sklosky-nl/sound-monitoring-mesh/sound level mesh hardware design.md

# Sound Level Mesh System - Hardware Design Document

## Document Information
- **Version:** 1.1
- **Date:** February 1, 2026
- **Status:** Production - Hardware Deployed
- **Author:** Hardware Engineering Team
- **Related Documents:** Sound Level Mesh System PRD, Architecture Document
- **Deployment Status:** Hardware received, assembled, and operational

---

## 1. Executive Summary

This document describes the hardware design for the Sound Level Mesh System monitoring devices. Each device consists of an ESP32-C3 microcontroller connected to an MH-ET LIVE INMP441 I2S Digital Microphone Module. The system requires 10 identical monitoring devices communicating via WiFi to a central web server.

### Hardware Components
- **Microcontroller:** ESP32-C3 Development Board (4MB flash)
- **Microphone Module:** MH-ET LIVE INMP441 I2S Digital Microphone Module
- **Power Supply:** USB Wall Charger Adapter (5V)
- **Power Cable:** USB-C Charging Cable
- **Enclosure:** Weather-resistant housing (to be determined)

### Purchased Hardware Status

**Hardware has been purchased and is awaiting delivery (Order Date: January 4, 2026).**

**Purchased Components:**
- ✅ **ESP32-C3 Development Boards:** 10 units (Simple Robot Store)
  - Model: ESP32-C3 Super Mini Development Board
  - Flash: 4MB
  - WiFi + Bluetooth
  - Total Cost: $21.79
  
- ✅ **MH-ET LIVE INMP441 I2S Microphone Modules:** 10 units (YX Electronic Components)
  - Omnidirectional MEMS microphone
  - I2S digital interface
  - Total Cost: $21.90 (10 × $2.19)
  
- ✅ **USB Wall Charger Adapters:** 10 units (Singyo Store)
  - 5 Pack × 2 orders = 10 total units
  - US Plug, Fast Charging
  - Total Cost: $8.62 (2 × $4.55)
  
- ✅ **USB-C Charging Cables:** 12 units (Super Deals Wholesale Factory Store)
  - 3 Pack × 4 orders = 12 total units
  - 1M length, 6A 100W Type C
  - Total Cost: $7.41 (4 × $1.99)

**Total Hardware Cost:** ~$59.72

**Note:** ESP32-C3 is a RISC-V based single-core microcontroller, different from the dual-core Xtensa-based ESP32. The specifications and pin assignments in this document will need to be verified against the ESP32-C3's actual capabilities and pinout.

---

## 2. Component Specifications

### 2.1 ESP32-C3 Microcontroller

#### Purchased Development Board
- **Model:** ESP32-C3 Super Mini Development Board (Purchased)
- **Chip:** ESP32-C3
- **Processor:** 
  - Single-core RISC-V microprocessor
  - Clock frequency: 160 MHz
  - 32-bit RISC-V architecture
- **Memory:**
  - Flash: 4 MB (as purchased)
  - SRAM: 400 KB
  - ROM: 384 KB
- **WiFi:**
  - 802.11 b/g/n (2.4 GHz)
  - WPA2/WPA3 support
- **Bluetooth:** Bluetooth 5.0 LE
- **GPIO Pins:** 21 programmable GPIO pins
- **I2S Interface:** Built-in I2S peripheral (to be verified)
- **Power:**
  - Operating voltage: 3.3V
  - Input voltage: 5V (via USB-C)
  - Current consumption: ~80-160 mA (active), ~10 µA (deep sleep)
- **USB:** USB-C interface
- **Dimensions:** Smaller form factor than standard ESP32 DevKit

**Important Note:** ESP32-C3 uses a different architecture (RISC-V) and has different pin assignments than the standard ESP32. The I2S pin assignments and GPIO numbers will need to be verified against the specific ESP32-C3 board's pinout once hardware is received.

#### ESP32-C3 Pinout (Relevant Pins - To Be Verified)

**Note:** Pin assignments below are preliminary and must be verified against the actual ESP32-C3 Super Mini board pinout once hardware is received.

- **Power Pins:**
  - USB-C: 5V input (via USB-C cable)
  - 3.3V: 3.3V output (if available on board)
  - GND: Ground
- **I2S Pins (for INMP441 connection - to be verified):**
  - I2S_DATA: TBD (verify GPIO pin)
  - I2S_WS: TBD (verify GPIO pin)
  - I2S_BCLK: TBD (verify GPIO pin)
- **Other Useful Pins:**
  - Boot button: TBD (verify GPIO pin)
  - Built-in LED: TBD (verify GPIO pin, if available)

**Action Required:** Once hardware is received, verify I2S peripheral availability and GPIO pin assignments for the ESP32-C3 Super Mini board.

### 2.2 MH-ET LIVE INMP441 I2S Digital Microphone Module

#### Module Specifications
- **Microphone Type:** Omnidirectional MEMS (Micro-Electro-Mechanical Systems)
- **Interface:** I2S digital output
- **Operating Voltage:** 1.8V - 3.3V (typically 3.3V)
- **Current Consumption:** ~1.2 mA typical
- **Sample Rate:** Up to 48 kHz
- **Bit Depth:** 24-bit
- **Signal-to-Noise Ratio (SNR):** 65 dB
- **Sensitivity:** -26 dBFS
- **Frequency Response:** 60 Hz - 15 kHz
- **Directional Pattern:** Omnidirectional
- **Operating Temperature:** -40°C to +85°C
- **Dimensions:** ~20mm × 20mm (module size)

#### Module Pinout
- **VDD:** Power supply (3.3V)
- **GND:** Ground
- **SCK:** Serial Clock (I2S Bit Clock)
- **WS:** Word Select (I2S Left/Right Clock)
- **SD:** Serial Data (I2S Data Output)
- **L/R:** Left/Right channel select (connect to GND for left/mono)

---

## 3. Wiring Diagram and Connections

### 3.1 INMP441 to ESP32-C3 Connection

**✅ Verified and Tested Configuration - Production Ready (February 2026)**

Pin assignments have been implemented, tested in firmware, and confirmed operational. System is actively deployed with "Sensor 01" transmitting measurements every 5 seconds at 76-77 dB ambient levels.

```
INMP441 Module          ESP32-C3 Board
─────────────────       ────────────────
VDD              ──────> 3.3V
GND              ──────> GND
SCK              ──────> GPIO 5 (I2S_BCLK)
WS               ──────> GPIO 6 (I2S_WS)
SD               ──────> GPIO 4 (I2S_DATA)
L/R              ──────> GND (for mono/left channel)
```

**Deployment Status:**
- ESP32-C3 Super Mini: ✅ Operational via USB-C power
- INMP441 Module: ✅ Wired and functional
- I2S Communication: ✅ Verified (16kHz sample rate, 32-bit containers)
- Audio Sampling: ✅ Active (76-77 dB ambient sound levels measured)
- WiFi Connectivity: ✅ Connected to backend server at 192.168.68.57:3000
- Configuration System: ✅ Dynamic config fetch on startup and periodic refresh
- Power: USB-C wall charger (from purchased batch)
- Device ID: "Sensor 01" (note: requires URL encoding for spaces)

**Important Notes for Additional Deployments:**
- Device IDs with spaces require URL encoding (%20) in firmware
- Configuration fetched automatically on startup from server
- Periodic configuration refresh every 100 measurements (~5 minutes)
- Default frequency bands: 20-200Hz, 200-2000Hz, 2000-8000Hz
- Per-device calibration offset applied (currently 1.0 dB for "Sensor 01")

### 3.2 Detailed Pin Connections (Verified)

| INMP441 Pin | ESP32-C3 Pin | Function | Notes |
|---|---|---|---|
| VDD | 3.3V | Power Supply | Connect to 3.3V output pin on ESP32-C3 board |
| GND | GND | Ground | Common ground |
| SCK | GPIO 5 | I2S Bit Clock | I2S_BCK - Serial Clock |
| WS | GPIO 6 | I2S Word Select | I2S_WS - Left/Right Clock |
| SD | GPIO 4 | I2S Serial Data | I2S_DATA - Serial Data Input |
| L/R | GND | Channel Select | Ground for left/mono channel |

**Status:** ✅ Verified and implemented in firmware. I2S peripheral confirmed functional on ESP32-C3.

### 3.3 Power Connections

**Option 1: USB Power (Recommended for Development)**
- Connect USB cable to ESP32 DevKit USB port
- Provides 5V power, regulated to 3.3V on board
- INMP441 powered from ESP32's 3.3V pin

**Option 2: External Power Supply**
- Connect 5V power supply to ESP32 VIN pin
- Ensure power supply can provide at least 500 mA
- INMP441 powered from ESP32's 3.3V pin

**Power Consumption Estimate:**
- ESP32 (active): ~80-260 mA @ 3.3V
- INMP441: ~1.2 mA @ 3.3V
- **Total:** ~100-270 mA @ 3.3V (or ~150-400 mA @ 5V input)

### 3.4 Wiring Diagram (Schematic View)

```
                    ┌─────────────────┐
                    │   ESP32 DevKit  │
                    │                 │
     USB/5V ───────>│ VIN             │
                    │                 │
                    │ 3.3V ───────────┼───┐
                    │                 │   │
                    │ GND ────────────┼───┼───┐
                    │                 │   │   │
                    │ GPIO 5 (BCLK) ──┼───┼───┼───┐
                    │                 │   │   │   │
                    │ GPIO 6 (WS) ────┼───┼───┼───┼───┐
                    │                 │   │   │   │   │
                    │ GPIO 4 (DATA) ──┼───┼───┼───┼───┼───┐
                    │                 │   │   │   │   │   │
                    └─────────────────┘   │   │   │   │   │
                                          │   │   │   │   │
                    ┌─────────────────┐  │   │   │   │   │
                    │  INMP441 Module  │  │   │   │   │   │
                    │                  │  │   │   │   │   │
                    │ VDD <────────────┘  │   │   │   │   │
                    │ GND <───────────────┘   │   │   │   │
                    │ SCK <────────────────────┘   │   │   │
                    │ WS  <───────────────────────┘   │   │
                    │ SD  <────────────────────────────┘   │
                    │ L/R <────────────────────────────────┘
                    │                  │
                    └──────────────────┘
```

---

## 4. Physical Layout and Assembly

### 4.1 Component Placement

**Recommended Layout:**
1. ESP32 DevKit board mounted on standoffs or PCB
2. INMP441 module positioned to minimize wire length
3. Keep I2S signal wires as short as possible (< 10 cm recommended)
4. Route power and ground wires together to reduce noise
5. Separate digital signals from power lines

### 4.2 Wire Specifications

**For I2S Signals (SCK, WS, SD):**
- **Type:** Twisted pair or shielded cable recommended
- **Length:** Keep under 10 cm if possible
- **Gauge:** 22-24 AWG
- **Shielding:** Optional but recommended for longer runs

**For Power (VDD, GND):**
- **Type:** Standard hookup wire
- **Length:** As needed for layout
- **Gauge:** 22-24 AWG
- **Note:** Use thicker wire (20 AWG) if power supply is far from module

### 4.3 Soldering vs. Breadboard

**Development/Prototyping:**
- Use breadboard or jumper wires for initial testing
- Allows easy reconfiguration and debugging

**Production:**
- Solder connections for reliability
- Use header pins or direct soldering
- Consider custom PCB for final design

### 4.4 Assembly Steps

**Note:** These steps assume ESP32-C3 I2S pin assignments have been verified. Pin numbers are placeholders until hardware is received.

1. **Prepare ESP32-C3:**
   - Ensure ESP32-C3 board is powered off
   - Identify I2S GPIO pins (to be verified), 3.3V output, and GND
   - Review ESP32-C3 Super Mini board pinout documentation

2. **Prepare INMP441:**
   - Identify module pins (VDD, GND, SCK, WS, SD, L/R)
   - Ensure module is clean and undamaged
   - Verify module is from purchased batch

3. **Make Connections:**
   - Connect power first: VDD to 3.3V, GND to GND
   - Connect I2S signals: SCK→GPIO 5, WS→GPIO 6, SD→GPIO 4
   - Connect L/R to GND for mono operation
   - Use purchased jumper wires for connections

4. **Verify Connections:**
   - Double-check all connections
   - Ensure no short circuits
   - Verify power polarity
   - Reference ESP32-C3 pinout diagram

5. **Power On:**
   - Connect USB-C cable to ESP32-C3
   - Connect USB-C cable to purchased wall charger
   - Plug wall charger into power outlet
   - Check for proper operation

---

## 5. I2S Configuration

### 5.1 I2S Bus Configuration

**For INMP441 Module:**
- **Sample Rate:** 16 kHz (recommended) or up to 48 kHz
- **Bit Depth:** 24-bit
- **Channel Format:** Mono (left channel)
- **Communication Format:** I2S (standard)
- **Bit Order:** MSB first
- **Clock Polarity:** Normal (data on falling edge)

### 5.2 ESP32 I2S Peripheral Settings

**I2S Configuration Parameters:**
- **Mode:** I2S_MODE_MASTER | I2S_MODE_RX (receive mode)
- **Sample Rate:** 16000 Hz (or 48000 Hz)
- **Bits Per Sample:** I2S_BITS_PER_SAMPLE_24BIT
- **Channel Format:** I2S_CHANNEL_FMT_ONLY_LEFT (mono)
- **Communication Format:** I2S_COMM_FORMAT_STAND_I2S
- **DMA Buffer Count:** 8
- **DMA Buffer Length:** 1024 bytes

### 5.3 Clock Configuration

**I2S Clock Calculation:**
- Bit Clock (BCLK) = Sample Rate × Bits Per Sample × Channels
- For 16 kHz, 24-bit, mono: BCLK = 16000 × 24 × 1 = 384 kHz
- For 48 kHz, 24-bit, mono: BCLK = 48000 × 24 × 1 = 1.152 MHz

**ESP32 I2S Clock:**
- ESP32 generates I2S clock internally
- Configure using I2S driver API
- Clock accuracy depends on APB clock (typically 80 MHz)

---

## 6. Power Supply Design

### 6.1 Power Requirements

**Total System Power:**
- ESP32-C3: 80-160 mA @ 3.3V (active mode)
- INMP441: 1.2 mA @ 3.3V
- **Total:** ~100-170 mA @ 3.3V

**Purchased Power Supply:**
- **USB Wall Charger Adapters:** 10 units purchased
  - 5V output via USB port
  - Fast charging capable
  - US Plug
  - Sufficient for ESP32-C3 + INMP441 power requirements

**Input Power:**
1. **USB-C Cable + Wall Charger (Purchased):** 
   - USB-C cable (1M, 6A 100W capable) connects ESP32-C3 to wall charger
   - Wall charger provides 5V power
   - 12 cables purchased (2 extra for spares)

### 6.2 Power Supply Considerations

**Voltage Regulation:**
- ESP32 DevKit includes onboard 3.3V regulator
- Accepts 5V input, regulates to 3.3V
- INMP441 requires stable 3.3V supply

**Power Filtering:**
- Add decoupling capacitors near INMP441:
  - 100 nF ceramic capacitor (VDD to GND)
  - 10 µF electrolytic capacitor (optional, for stability)

**Power Consumption Optimization:**
- ESP32 can enter light sleep between measurements
- Reduces average power consumption
- INMP441 remains active during sleep (low power)

### 6.3 Battery Operation (Optional)

**If Battery-Powered:**
- Use 3.7V Li-ion battery (single cell)
- Requires voltage regulator to 3.3V
- Add battery management circuit (BMS)
- Consider power consumption for battery life calculation

---

## 7. Enclosure and Environmental Considerations

### 7.1 Enclosure Requirements

**Physical Protection:**
- Weather-resistant housing (IP54 minimum, IP65 recommended)
- Protection from dust and moisture
- Ventilation for microphone (acoustic port)
- Access to USB port or power connector

**Acoustic Considerations:**
- Microphone should have clear path to environment
- Acoustic port/opening for sound waves
- Avoid blocking microphone with enclosure material
- Consider wind protection (foam windscreen)

**Thermal Management:**
- ESP32 can generate heat during operation
- Ensure adequate ventilation
- Operating temperature: 0°C to +50°C (typical)

### 7.2 Mounting Considerations

**Installation:**
- Secure mounting to prevent vibration
- Position microphone away from noise sources
- Consider height and orientation for optimal sound capture
- Ensure WiFi antenna has clear line of sight

**Cable Management:**
- Secure power cable to prevent disconnection
- Protect cables from environmental damage
- Use weather-resistant cable if exposed

---

## 8. Testing and Verification

### 8.1 Initial Testing

**Power-On Test:**
1. Connect power supply
2. Verify ESP32 boots (LED indicators if available)
3. Check WiFi connectivity
4. Verify I2S communication with INMP441

**Audio Test:**
1. Send test signal or use known sound source
2. Verify audio data is received via I2S
3. Check sample rate and bit depth
4. Verify FFT processing produces expected results

### 8.2 Functional Testing

**Measurement Accuracy:**
- Compare with calibrated reference sound level meter
- Test at various sound levels (30-130 dB)
- Verify frequency band measurements
- Test calibration offset application

**System Integration:**
- Verify data transmission to central server
- Test configuration retrieval
- Verify real-time monitoring
- Test device registration

### 8.3 Environmental Testing

**Temperature:**
- Test at operating temperature range
- Verify performance at extremes

**Humidity:**
- Test in high humidity conditions
- Verify enclosure protection

**Vibration:**
- Test with mechanical vibration
- Verify connections remain secure

---

## 9. Bill of Materials (BOM)

### 9.1 Required Components (Per Device)

| Component | Part Number/Description | Quantity | Status |
|---|---|---|---|
| ESP32-C3 Board | ESP32-C3 Super Mini (4MB flash) | 1 | ✅ Purchased (10 units) |
| INMP441 Module | MH-ET LIVE INMP441 | 1 | ✅ Purchased (10 units) |
| USB-C Cable | Type C, 1M, 6A 100W | 1 | ✅ Purchased (12 units total) |
| USB Wall Charger | 5V Fast Charging, US Plug | 1 | ✅ Purchased (10 units) |
| Jumper Wires | 22-24 AWG | 6 | ⏳ To be purchased |
| Enclosure | Weather-resistant | 1 | ⏳ To be determined |
| Standoffs | M3, 10mm | 4 | ⏳ Optional, to be purchased |

**Purchased Hardware Summary:**
- ✅ All 10 ESP32-C3 development boards
- ✅ All 10 INMP441 microphone modules
- ✅ All 10 USB wall chargers (with 2 extra cables)
- ⏳ Jumper wires and enclosures still needed

### 9.2 Optional Components

| Component | Description | Quantity | Notes |
|---|---|---|---|
| Decoupling Capacitors | 100 nF ceramic | 2 | Power filtering |
| LED Indicator | 3mm LED | 1 | Status indication |
| Resistor | 220Ω | 1 | For LED (if used) |
| Antenna Extension | WiFi antenna cable | 1 | If needed for range |

### 9.3 Tools Required

- Soldering iron (if soldering connections)
- Multimeter (for testing)
- Wire strippers
- Breadboard (for prototyping)
- Oscilloscope (optional, for signal verification)

---

## 10. Troubleshooting

### 10.1 Common Issues

**No Audio Data:**
- Check I2S pin connections
- Verify I2S configuration matches INMP441 specs
- Check power supply to INMP441 (3.3V)
- Verify sample rate and bit depth settings

**Poor Audio Quality:**
- Check for loose connections
- Verify power supply stability
- Check for electrical interference
- Ensure proper I2S clock configuration

**WiFi Connection Issues:**
- Verify WiFi credentials
- Check signal strength
- Ensure ESP32 antenna is not blocked
- Verify network configuration

**Power Issues:**
- Check power supply voltage
- Verify current capacity (minimum 500 mA)
- Check for short circuits
- Verify ground connections

### 10.2 Diagnostic Procedures

**I2S Signal Verification (if I2S available on ESP32-C3):**
1. Verify I2S peripheral is available on ESP32-C3
2. Use oscilloscope to check I2S signals (if available)
3. Verify clock frequency matches configuration
4. Check data signal for activity
5. Verify word select timing

**Power Verification:**
1. Measure voltage at INMP441 VDD pin (should be 3.3V)
2. Check current consumption
3. Verify no voltage drops under load

**Communication Test:**
1. Use serial monitor to check ESP32-C3 output
2. Verify I2S data reception (if I2S peripheral available)
3. Check for error messages
4. Test WiFi connectivity
5. Test data transmission to server

---

## 11. Safety Considerations

### 11.1 Electrical Safety

- Ensure proper power supply voltage (5V for ESP32, 3.3V for INMP441)
- Avoid short circuits between power and ground
- Use appropriate wire gauge for current requirements
- Verify polarity before connecting power

### 11.2 Environmental Safety

- Ensure enclosure provides adequate protection
- Avoid exposure to water or excessive moisture
- Protect from extreme temperatures
- Secure mounting to prevent falling

### 11.3 Operational Safety

- Follow manufacturer specifications
- Do not exceed maximum ratings
- Allow adequate ventilation for heat dissipation
- Regular inspection and maintenance

---

## 12. Future Enhancements

### 12.1 Potential Improvements

- **Custom PCB:** Design dedicated PCB for production
- **Battery Power:** Add battery support with power management
- **Additional Sensors:** Temperature, humidity sensors
- **Status LEDs:** Visual indicators for device status
- **External Antenna:** Improved WiFi range
- **Power Management:** Low-power modes for extended operation

### 12.2 Scalability Considerations

- Design for easy assembly and maintenance
- Standardize connections for consistency
- Document assembly procedures
- Create assembly jigs if producing multiple units

---

## 13. Appendix

### A. Pin Reference Tables

**ESP32-C3 GPIO Pin Functions (Verified):**
- I2S_DATA: GPIO 4 (Input) - Serial Data from INMP441
- I2S_BCLK: GPIO 5 (Output) - Bit Clock to INMP441
- I2S_WS: GPIO 6 (Output) - Word Select to INMP441
- Boot button: GPIO 9 (Input, pull-up) - Standard on ESP32-C3
- Built-in LED: GPIO 8 (Output) - Standard on ESP32-C3 Super Mini

**Note:** Pin assignments verified and implemented in firmware. I2S peripheral confirmed functional on ESP32-C3.

**INMP441 Pin Functions:**
- VDD: Power (3.3V)
- GND: Ground
- SCK: Serial Clock (Input)
- WS: Word Select (Input)
- SD: Serial Data (Output)
- L/R: Channel Select (Input, connect to GND)

### B. I2S Timing Diagram

```
BCLK:  _|‾|_|‾|_|‾|_|‾|_|‾|_|‾|_|‾|_|‾|_
       |   |   |   |   |   |   |   |   |
WS:    ‾‾‾‾‾‾‾‾‾‾‾‾‾‾‾‾‾‾‾‾‾‾‾‾‾‾‾‾‾‾‾‾
       (Left Channel)    (Right Channel)
SD:    MSB ────────────────> LSB
       (24-bit data word)
```

### C. References

- ESP32 Technical Reference Manual: Espressif Systems
- ESP-IDF Programming Guide: Espressif Systems
- INMP441 Datasheet: InvenSense
- MH-ET LIVE INMP441 Module Documentation
- I2S Bus Specification

### D. Related Documents

- Sound Level Mesh System PRD
- Sound Level Mesh Architecture Document
- Firmware Development Guide (to be created)
- Assembly Instructions (to be created)

---

## Document Approval

| Role | Name | Signature | Date |
|---|---|---|---|
| Hardware Engineer | | | |
| Electrical Engineer | | | |
| System Architect | | | |

---

**Document Status:** Draft - Pending Review and Approval
