sklosky-nl/sound-monitoring-mesh/PRE_COMMIT_CHECKLIST.md

# Pre-Commit Security Checklist

✅ **All sensitive information has been protected**

## Files Excluded from Git

### 1. WiFi Credentials & Configuration
- ✅ `firmware/sound-level-sensor/sdkconfig` - Contains WiFi SSID "YOUR_WIFI_SSID" and password
- ✅ Template provided: `sdkconfig.example` with safe defaults

### 2. Backend Data Directories
- ✅ `backend/data/devices/` - Device registration JSON files
- ✅ `backend/data/measurements/` - Measurement data files
- ✅ `backend/data/alerts/` - Alert configuration and history
- ✅ `backend/data/logs/` - Server log files

### 3. Other Sensitive Files
- ✅ `screenlog.0` - Terminal session log
- ✅ `.env` files - Environment variables

## Files Updated to Remove Sensitive Defaults

### Kconfig.projbuild
- ❌ **Before:** `CONFIG_WIFI_SSID="YOUR_WIFI_SSID"`
- ✅ **After:** `CONFIG_WIFI_SSID="YourWiFiSSID"`

- ❌ **Before:** `CONFIG_WIFI_PASSWORD="REDACTED"`
- ✅ **After:** `CONFIG_WIFI_PASSWORD="YourWiFiPassword"`

- ❌ **Before:** `CONFIG_SERVER_URL="http://192.168.68.67:3000"`
- ✅ **After:** `CONFIG_SERVER_URL="http://192.168.1.100:3000"` (generic)

## New Security Documentation

### SECURITY.md
- Complete guide for securing the project
- Setup instructions for new users
- What's safe to commit vs. what to exclude
- Recovery procedures for accidentally committed secrets

### README.md
- Added 🔒 Security section
- Links to SECURITY.md
- Setup instructions

### sdkconfig.example
- Template configuration file
- Safe placeholder values
- Instructions for users to copy and configure

## Gitignore Patterns Added

```gitignore
# ESP32 configuration (contains WiFi credentials)
firmware/**/sdkconfig
firmware/**/sdkconfig.old
!firmware/**/sdkconfig.defaults

# Backend data directories
backend/data/measurements/
backend/data/devices/
backend/data/alerts/
backend/data/logs/

# Screen logs
screenlog.*
```

## Verification Commands

Run these before committing:

```bash
# Check what files git will track
git status

# Verify sdkconfig is ignored
git check-ignore firmware/sound-level-sensor/sdkconfig
# Should output: firmware/sound-level-sensor/sdkconfig

# Search for any passwords or SSIDs in tracked files
git grep -i "YOUR_WIFI_SSID\|REDACTED" -- ':!.gitignore' ':!*.md'
# Should return no results

# Check what would be added
git add -n .
```

## Safe to Commit

✅ All source code files (*.c, *.js, *.html, *.css)
✅ Configuration templates (sdkconfig.example, sdkconfig.defaults)
✅ Documentation files (*.md)
✅ Package manifests (package.json, CMakeLists.txt)
✅ Build scripts

## Status: READY FOR PUBLIC GITHUB ✅

All sensitive information has been:
- Excluded via .gitignore
- Replaced with safe defaults in templates
- Documented in SECURITY.md

**The repository is now safe to commit to a public GitHub repository.**
