sklosky-nl/sound-monitoring-mesh/enclosure/WIFI_SIGNAL_SOLUTIONS.md

# WiFi Signal Solutions for PETG Enclosure

> **✅ FINAL SOLUTION IMPLEMENTED:** After analysis and testing, the project uses **microphone foam windscreens** as the complete enclosure. This simple solution provides dust protection, RF transparency (<0.5 dB loss), acoustic transparency, and costs ~$1-2 per device. See [README.md](README.md) for implementation details.
>
> This document is retained for reference on RF attenuation issues and alternative solutions that were considered.

---

## Problem
PETG enclosures can block WiFi signals (2.4 GHz), especially when fully enclosed. This causes connectivity issues for ESP32 devices in dusty environments.

## Root Cause
- PETG attenuates 2.4 GHz signals by 3-8 dB per wall thickness
- Fully enclosed design creates partial Faraday cage effect
- ESP32-C3 has PCB antenna requiring clear RF path

---

## Solutions (Ranked by Effectiveness)

### 🥇 Solution 1: External Antenna (Most Reliable)
**Best for harsh dusty environments**

**Implementation:**
1. Add U.FL/IPEX connector to ESP32-C3
2. Route antenna cable through sealed cable gland (PG7, 3mm)
3. Mount 2.4 GHz antenna outside enclosure
4. Maintains full IP65+ dust/waterproof rating

**Parts Needed:**
- U.FL/IPEX to RP-SMA pigtail cable (10cm) - $3
- 2.4 GHz WiFi antenna with RP-SMA - $4
- PG7 cable gland - $2
- Total: ~$9/device

**Pros:**
- ✅ Full signal strength maintained
- ✅ Keeps complete dust seal
- ✅ Works in extreme environments
- ✅ Professional solution

**Cons:**
- ⚠️ Requires antenna connector soldering
- ⚠️ Slightly more complex assembly

---

### 🥈 Solution 2: RF Window in Enclosure
**Good balance of dust protection and signal**

**Implementation:**
1. Modify STL/F3D: Cut 30mm × 30mm opening above ESP32 location
2. Cover with thin polycarbonate sheet (0.5mm) or fine mesh
3. Seal edges with silicone gasket or adhesive
4. Maintains dust protection with <1 dB signal loss

**Design Changes:**
```
Enclosure modifications:
- Top panel: 30×30mm cutout centered over ESP32
- Add retaining lip for cover material
- Use stainless steel mesh (40-60 mesh) OR
- Use thin polycarbonate/acrylic window
```

**Pros:**
- ✅ No electronics modification needed
- ✅ Maintains most dust protection
- ✅ Simple implementation
- ✅ Minimal signal loss

**Cons:**
- ⚠️ Requires enclosure redesign/modification
- ⚠️ Slight dust ingress potential at window

---

### 🥉 Solution 3: Ventilation with Dust Filtering
**For moderate dust environments**

**Implementation:**
1. Add 6-8 holes (10-15mm diameter) around top perimeter
2. Cover with one of:
   - Stainless steel mesh (250-425 micron / 40-60 mesh)
   - Gore-Tex membrane vent patches
   - Sintered metal dust filters
3. Position holes for cross-ventilation

**Recommended Mesh Specifications:**
- **Mesh size:** 40-60 mesh (250-425 micron openings)
- **Material:** Stainless steel 316 (corrosion resistant)
- **Installation:** Epoxy or hot-glue to inside of enclosure

**Pros:**
- ✅ Good RF transparency
- ✅ Allows heat dissipation
- ✅ Simple to implement
- ✅ No electronics changes

**Cons:**
- ⚠️ Fine dust can still enter over time
- ⚠️ Not suitable for very dusty environments
- ⚠️ Requires filter maintenance/replacement

---

### 🔧 Solution 4: Material Change
**For new builds**

**Instead of PETG, use:**
1. **ABS** - Better RF transparency, slightly less dust resistant
2. **PLA** - Good RF, but lower heat tolerance
3. **Polycarbonate** - Excellent RF transparency and durability
4. **Hybrid:** PETG base + thin ABS/PLA top section

**Print Settings for RF Transparency:**
- Thin walls (1-2 perimeters, 0.8-1.6mm)
- Minimal infill in RF critical areas (10-20%)
- Avoid thick solid sections near antenna

---

## Quick Verification Tests

### Test 1: Confirm Enclosure is Blocking Signal
1. Remove device from enclosure
2. Monitor backend logs: `tail -f backend/data/logs/combined.log | grep "POST /api/data"`
3. Device should reconnect within 30-60 seconds
4. If it reconnects → enclosure is the problem

### Test 2: Measure Signal Strength (if device has serial access)
```c
// Add to ESP32 firmware:
int8_t rssi = WiFi.RSSI();
ESP_LOGI(TAG, "WiFi RSSI: %d dBm", rssi);
```
- Good signal: -30 to -67 dBm
- Fair signal: -68 to -80 dBm  
- Poor signal: < -80 dBm (likely to disconnect)

### Test 3: Drill Test Holes
1. Drill 3-4 small holes (5mm) in top of enclosure
2. Monitor if device reconnects
3. If successful → proves ventilation solution will work

---

## Recommended Implementation Plan

### For Your Dusty Environment:

**Option A: Quick Fix (Today)**
1. Drill 8× 12mm holes in top/sides of current enclosure
2. Cover with stainless steel mesh (from hardware store)
3. Hot glue or epoxy mesh in place
4. Cost: $5, Time: 30 minutes

**Option B: Professional Solution (Best Long-term)**
1. Order external antenna kit (~$10)
2. Solder U.FL connector to ESP32 (or use pre-made version)
3. Modify enclosure with cable gland pass-through
4. Mount antenna on exterior
5. Cost: $10/device, Time: 45 minutes per device

**Option C: Redesign Enclosure (For multiple devices)**
1. Modify .f3d design with RF window or ventilation
2. Add mesh/filter mounting features
3. Print new enclosures for all devices
4. Cost: ~$3-5/device (filament + mesh)
5. Time: 2 hours design + printing time

---

## Stainless Steel Mesh Specifications

**Recommended Mesh for Dust Protection + RF Transparency:**
- **Type:** Woven wire mesh
- **Material:** Stainless steel 316 or 304
- **Mesh Count:** 40-60 mesh (40-60 wires per inch)
- **Wire Diameter:** 0.18-0.25mm
- **Opening Size:** 250-425 microns
- **Blocks:** Particles > 250 microns (most dust)
- **Passes:** 2.4 GHz WiFi signals (wavelength: 125mm)

**Where to Buy:**
- Amazon: "40 mesh stainless steel screen"
- McMaster-Carr: Part #9318T53
- Local hardware store: Stainless steel window screen

---

## Notes from Build Experience

⚠️ **Discovered Issues:**
- Lid fit required heat gun adjustment (mentioned in main README)
- PETG thickness needed for dust protection blocks WiFi
- ESP32-C3 SuperMini uses PCB antenna (surface mount, no external connector stock)

**Lessons Learned:**
- Test RF connectivity BEFORE final enclosure design
- Consider antenna placement in CAD design phase
- Ventilation is always better than complete sealing for electronics
- PETG is great for mechanical parts, poor for RF applications
